stefanofinetti/MF_RMP_Panel/3D FIles/V5.1/CopriLed-CopriLed-1.5mm.stl

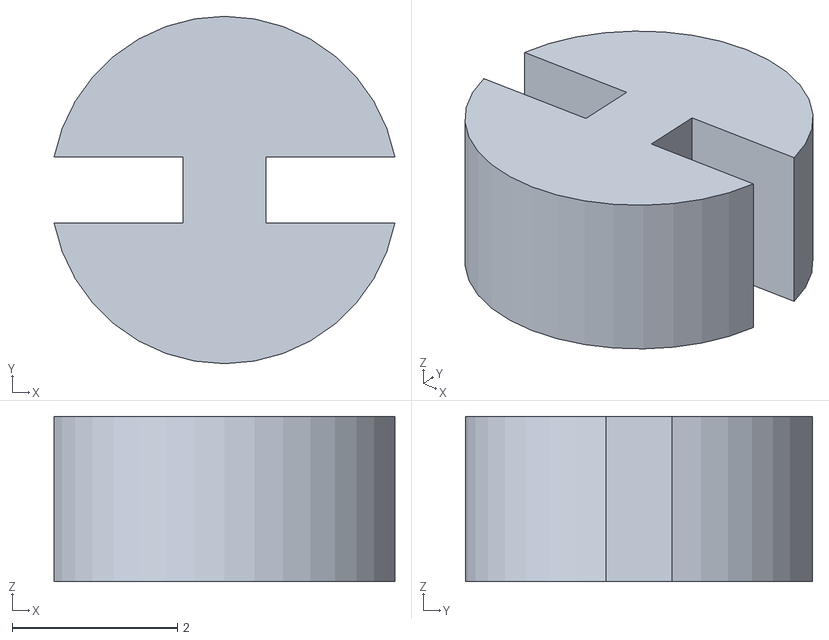
[picture p27: CAD file, 2026-10-05]
3D FIles/V5.1/CopriLed-CopriLed-1.5mm.stl
4.12 x 4.20 x 2.00
