stefanofinetti/MF_RMP_Panel/3D FIles/RMP_Panel-StandbyDisplayCase.stl

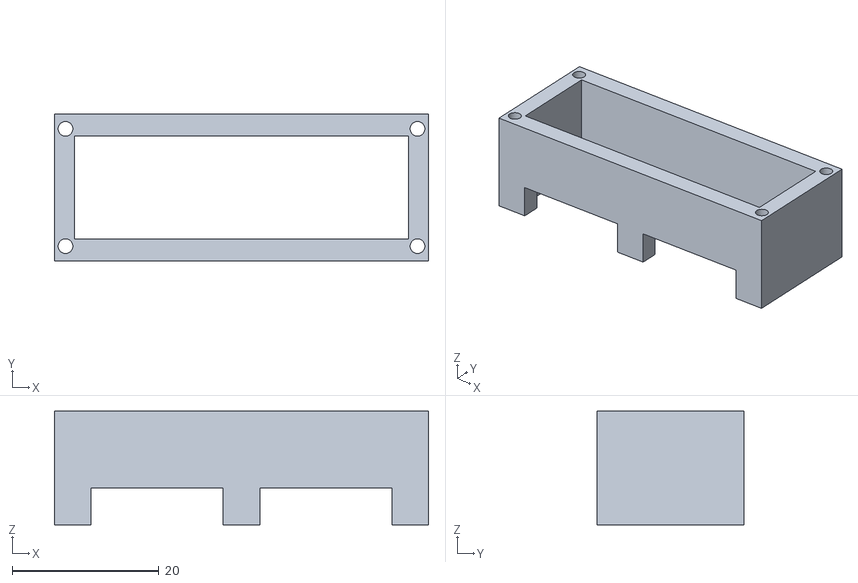
[picture p29: CAD file, 2026-10-05]
3D FIles/RMP_Panel-StandbyDisplayCase.stl
51.0 x 20.0 x 15.5
