stefanofinetti/MF_RMP_Panel/3D FIles/V5.1/RMP_Knob-LowerCircle_KHz.stl

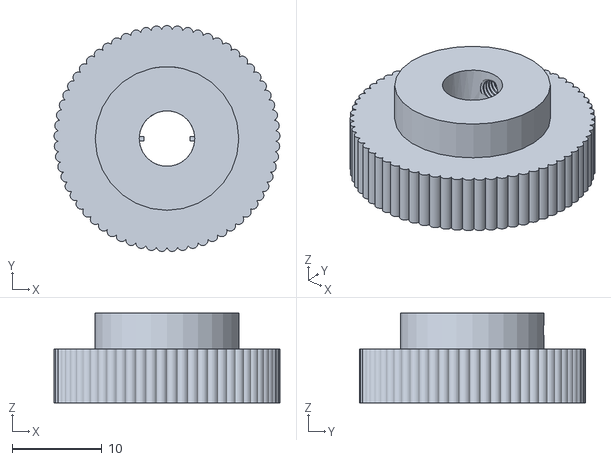
[picture p30: CAD file, 2026-10-05]
3D FIles/V5.1/RMP_Knob-LowerCircle_KHz.stl
25.2 x 25.2 x 10.0
