stefanofinetti/MF_RMP_Panel/3D FIles/RMP_Panel-Labels.stl

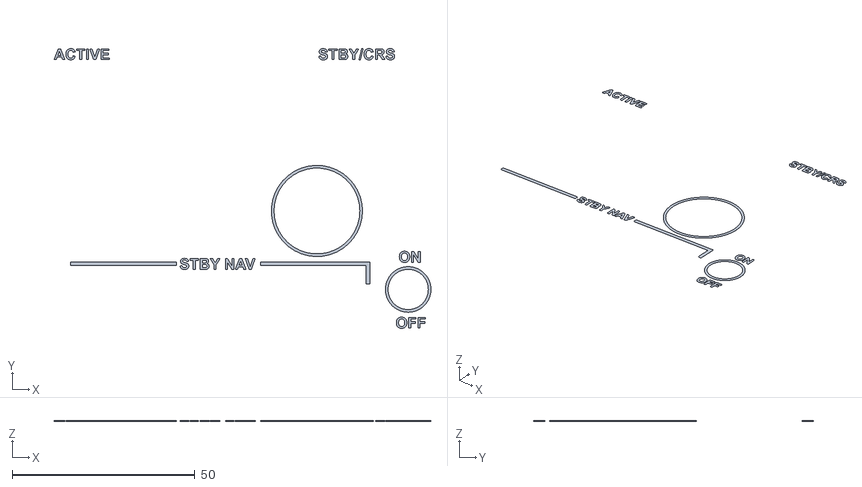
[picture p31: CAD file, 2026-10-05]
3D FIles/RMP_Panel-Labels.stl
103.3 x 76.7 x 0.2
