stefanofinetti/MF_RMP_Panel/3D FIles/RMP_Panel.3mf

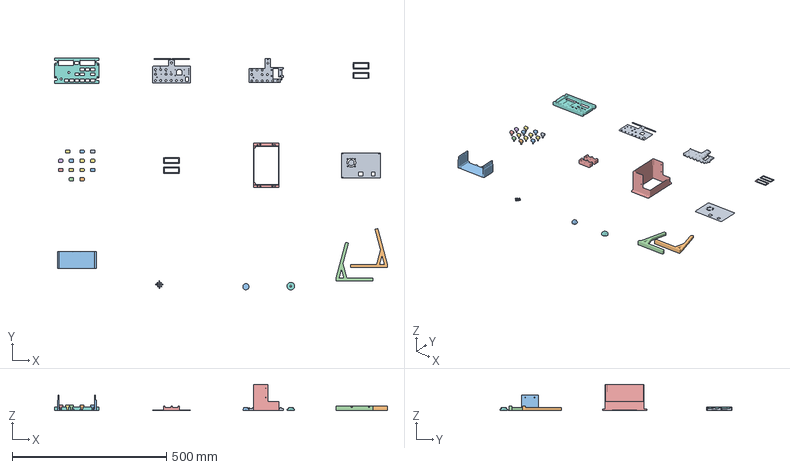
[picture p33: CAD file, 2026-10-05]
3D FIles/RMP_Panel.3mf
1079.3 x 752.2 x 85.0 mm
RMP_Button- ADF Black Parts
RMP_Panel-BasePad076 x 2
RMP_Knob-UpperCircle_MHz.stl
RMP_Panel-RMP Case.stl
CopriLed-CopriLed-1.5mm.stl x 13
VHF1_Button-Black Parts
RMP_Panel-RMP Bottom (USB and power holes).stl
RMP_Button- VOR Black Parts
RMP_Panel-ActiveDisplayCase.stl
RMP_Button- BFO Black Parts
RMP_Panel-Led Mask (print x2).stl x 2
RMP_Button-VHF2 Black Parts
RMP_Panel-StandbyDisplayCase.stl
RMP_Button-XFER Black Parts
RMP_Panel-LED PCB.stl
RMP_Button-VHF3 Black Parts
RMP_Button-HF1 Black Parts
RMP_Knob-LowerCircle_KHz.stl
RMP_Panel-PCB Separator.stl
RMP_Button-HF2 Black Parts
RMP_Panel-ArduinoSupport.stl
RMP_Button-AM Black Parts
RMP_Button-NAV Black Parts
RMP_Button-ILS Black Parts
RMP_Button-MLS BlackParts
RMP_Panel-BlackElements
