stefanofinetti/MF_RMP_Panel/3D FIles/V5.1/RMP_Panel-TransparentElements.stl

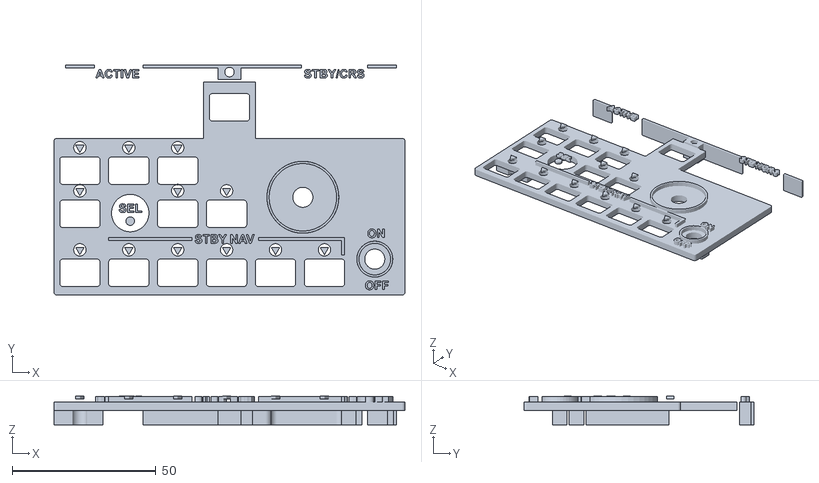
[picture p34: CAD file, 2026-10-05]
3D FIles/V5.1/RMP_Panel-TransparentElements.stl
122.0 x 80.0 x 10.0
