stefanofinetti/MF_RMP_Panel/3D FIles/Buttons/RMP_Button- BFO White Parts.stl

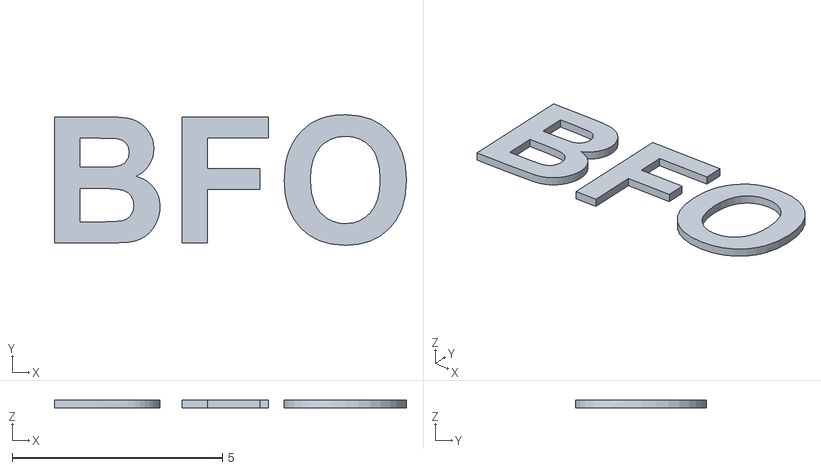
[picture p35: CAD file, 2026-10-05]
3D FIles/Buttons/RMP_Button- BFO White Parts.stl
8.36 x 3.10 x 0.2
