stefanofinetti/MF_RMP_Panel/3D FIles/Labels.stl

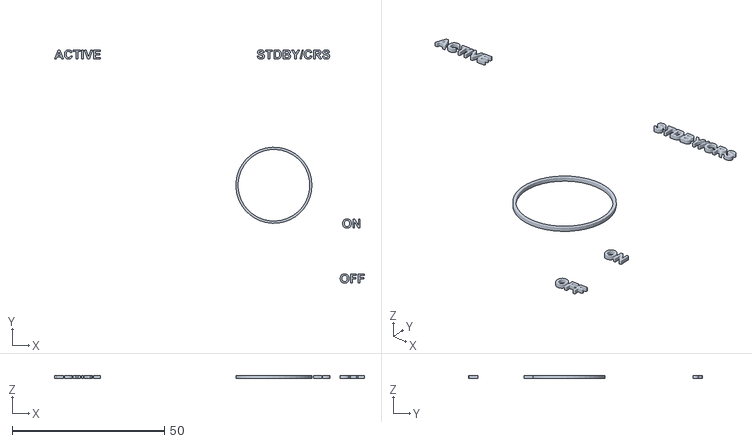
[picture p36: CAD file, 2026-10-05]
3D FIles/Labels.stl
101.8 x 76.7 x 1.00
