stefanofinetti/MF_RMP_Panel/3D FIles/Buttons/RMP_Button-XFER White Parts.stl

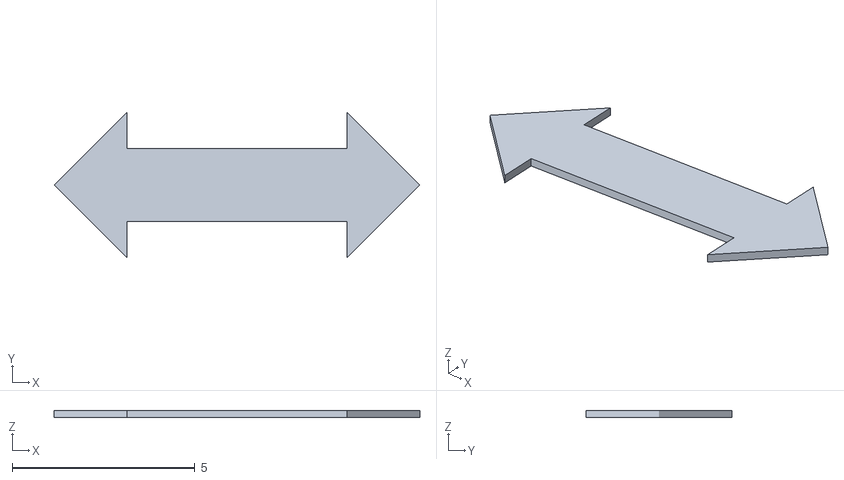
[picture p37: CAD file, 2026-10-05]
3D FIles/Buttons/RMP_Button-XFER White Parts.stl
10.0 x 4.00 x 0.2
