stefanofinetti/MF_RMP_Panel/3D FIles/RMP_Panel-LED PCB.stl

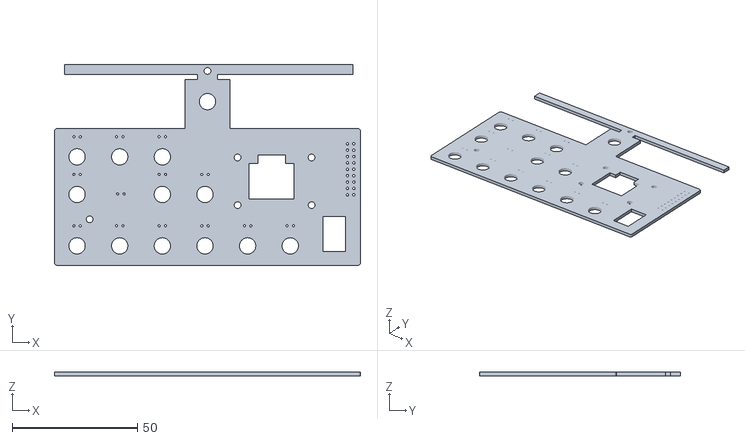
[picture p38: CAD file, 2026-10-05]
3D FIles/RMP_Panel-LED PCB.stl
122.0 x 80.0 x 1.51
