stefanofinetti/MF_RMP_Panel/3D FIles/Buttons/RMP_Button-NAV White Parts.stl

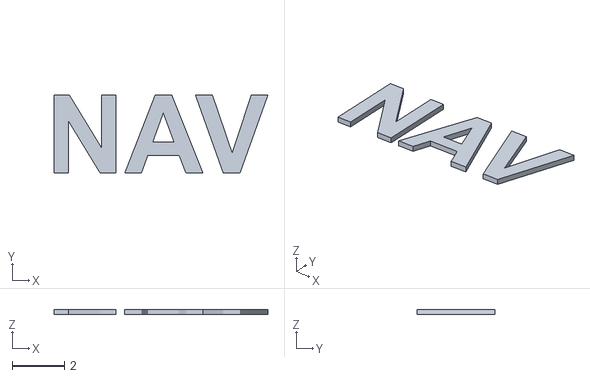
[picture p39: CAD file, 2026-10-05]
3D FIles/Buttons/RMP_Button-NAV White Parts.stl
8.22 x 3.00 x 0.2
