stefanofinetti/MF_RMP_Panel/3D FIles/RMP_Panel-TransparentElements.stl

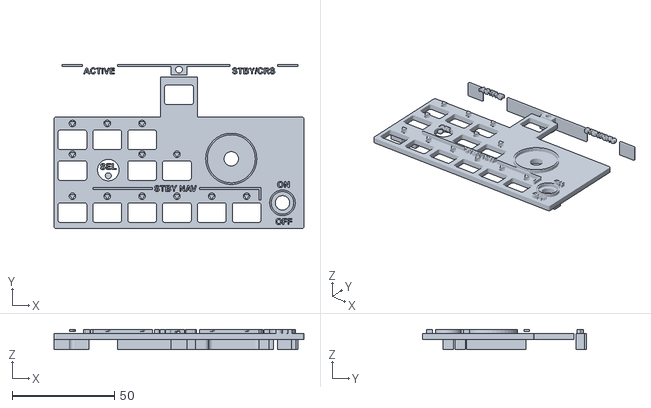
[picture p40: CAD file, 2026-10-05]
3D FIles/RMP_Panel-TransparentElements.stl
122.0 x 80.0 x 10.0
