stefanofinetti/MF_RMP_Panel/3D FIles/RMP_Button.FCStd

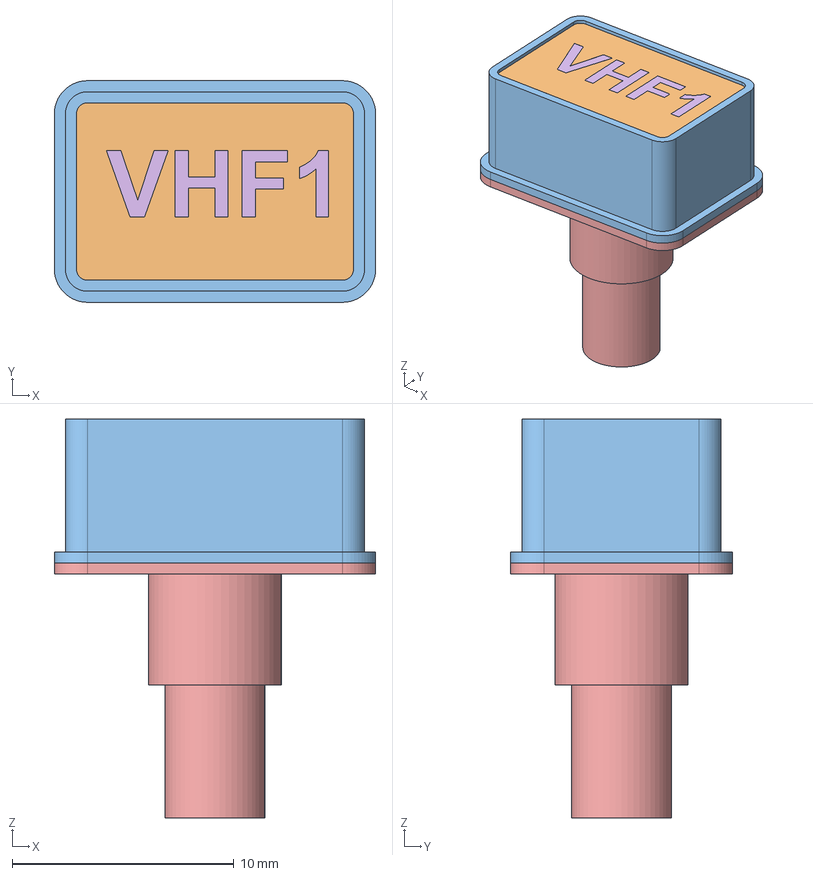
[picture p41: CAD file, 2026-10-05]
3D FIles/RMP_Button.FCStd
14.5 x 10.0 x 18.0 mm
Button Upper Layer
Cutout
Button Casing
LabelTransparent
Button Transparent Block
LabelWhite
