stefanofinetti/MF_RMP_Panel/3D FIles/V5.1/RMP_Panel-Left SupportPad075.stl

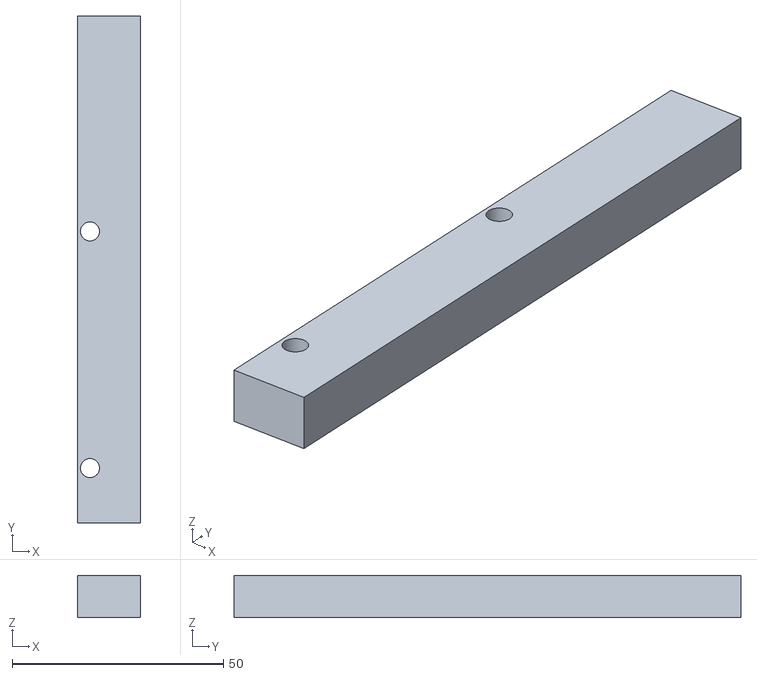
[picture p42: CAD file, 2026-10-05]
3D FIles/V5.1/RMP_Panel-Left SupportPad075.stl
15.0 x 120.0 x 10.0
