stefanofinetti/MF_RMP_Panel/3D FIles/RMP_Panel-Led Mask (print x2).stl

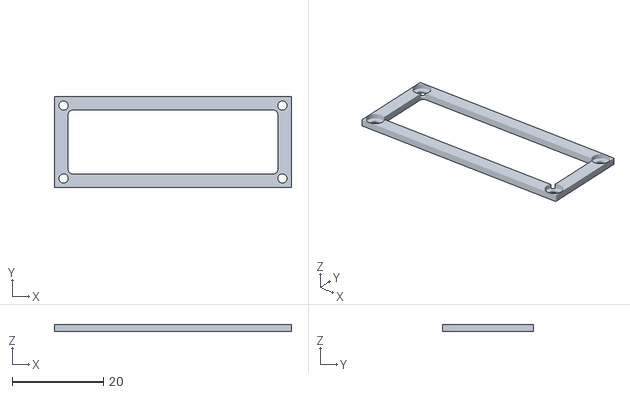
[picture p44: CAD file, 2026-10-05]
3D FIles/RMP_Panel-Led Mask (print x2).stl
52.0 x 20.0 x 1.50
