stefanofinetti/MF_RMP_Panel/3D FIles/V5.1/RMP_Panel-BasePad076.stl

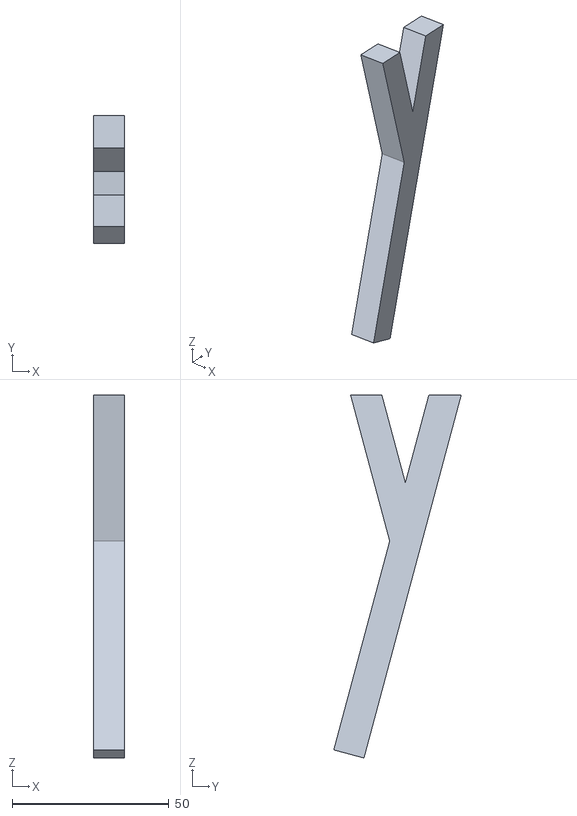
[picture p45: CAD file, 2026-10-05]
3D FIles/V5.1/RMP_Panel-BasePad076.stl
10.0 x 40.7 x 115.9
