stefanofinetti/MF_RMP_Panel/3D FIles/Buttons/RMP_Button-HF2 Black Parts.stl

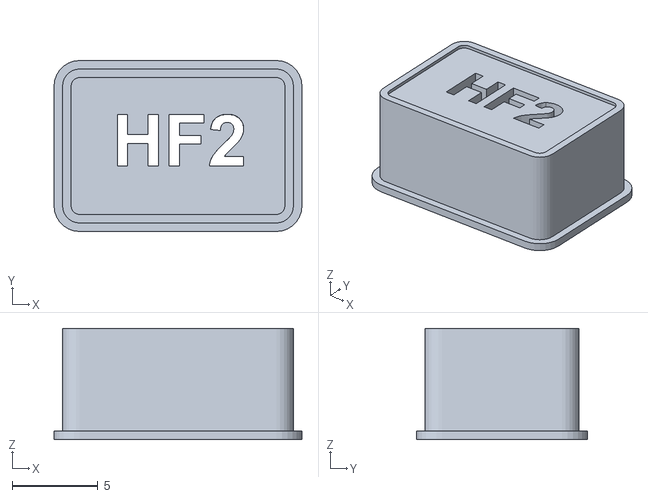
[picture p46: CAD file, 2026-10-05]
3D FIles/Buttons/RMP_Button-HF2 Black Parts.stl
14.5 x 10.0 x 6.50
