stefanofinetti/MF_RMP_Panel/3D FIles/RMP_LEDS1.FCStd

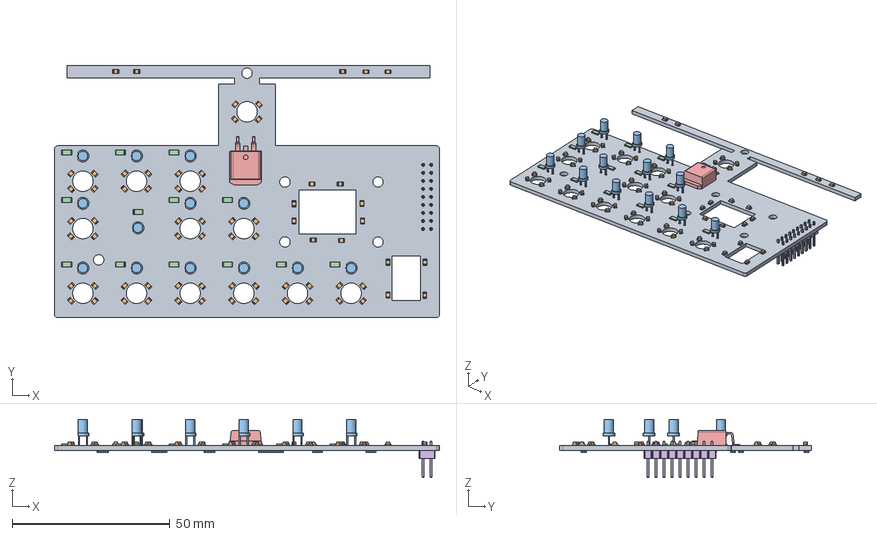
[picture p47: CAD file, 2026-10-05]
3D FIles/RMP_LEDS1.FCStd
122.0 x 80.0 x 18.4 mm
Pcb_f16.[solid]
D20_LED_0805_2012Metric_1352afc11da3 x 69
D74_LED_D3.0mm_FlatTop_4eb7fb95d653 x 13
R25_R_1206_3216Metric_ccd3cef4aefe x 29
Q1_IRLZ44NSTRLPBF_374ea2df2183
J1_PinHeader_2x09_P254mm_Vertical_5930f4462cf5
