stefanofinetti/MF_RMP_Panel/3D FIles/Buttons/RMP_Button-HF2 White Parts.stl

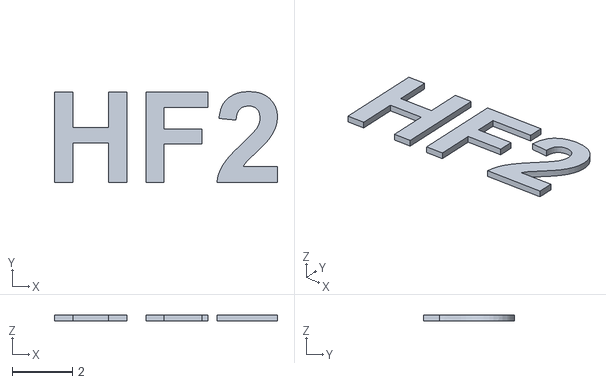
[picture p48: CAD file, 2026-10-05]
3D FIles/Buttons/RMP_Button-HF2 White Parts.stl
7.39 x 3.02 x 0.2
