stefanofinetti/MF_RMP_Panel/3D FIles/FrontPanelWithWritings.stl

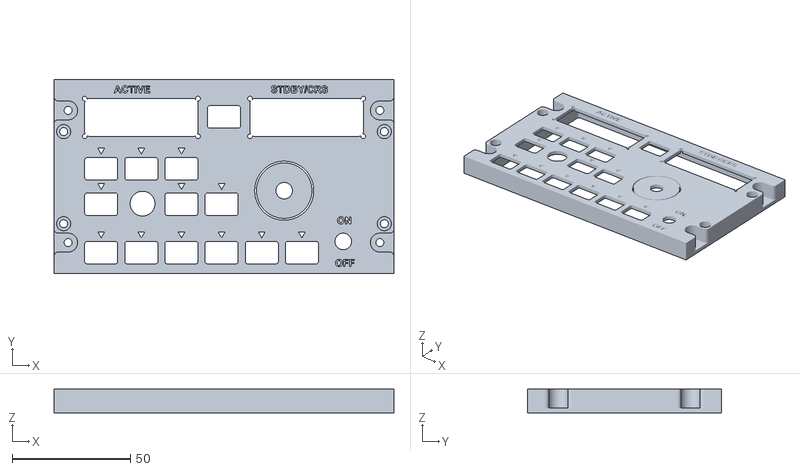
[picture p49: CAD file, 2026-10-05]
3D FIles/FrontPanelWithWritings.stl
144.0 x 82.0 x 10.0
