stefanofinetti/MF_RMP_Panel/3D FIles/Buttons/RMP_Button-VHF2 Transparent Parts.stl

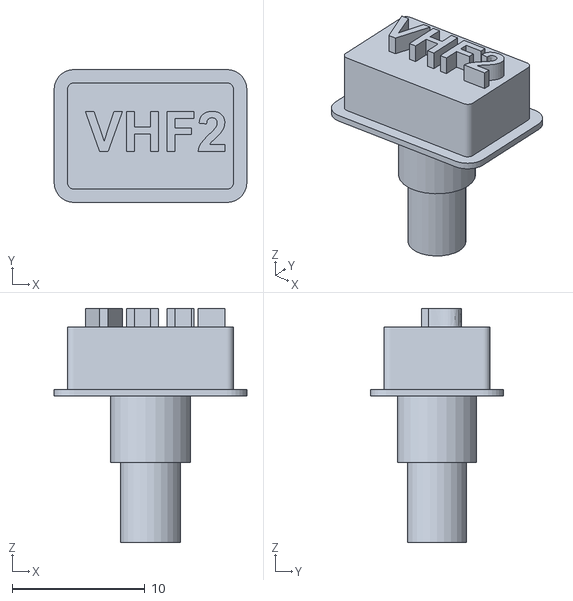
[picture p50: CAD file, 2026-10-05]
3D FIles/Buttons/RMP_Button-VHF2 Transparent Parts.stl
14.5 x 10.0 x 17.6
