stefanofinetti/MF_RMP_Panel/3D FIles/Buttons/RMP_Button- VOR White Parts.stl

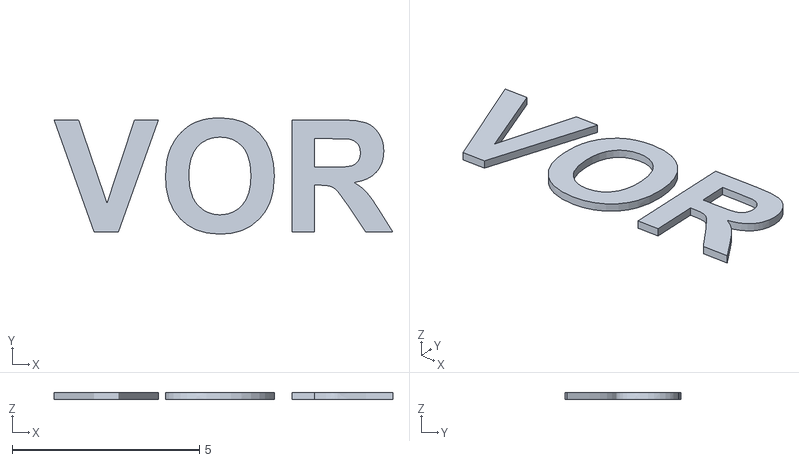
[picture p51: CAD file, 2026-10-05]
3D FIles/Buttons/RMP_Button- VOR White Parts.stl
9.05 x 3.10 x 0.2
