stefanofinetti/MF_RMP_Panel/3D FIles/Buttons/RMP_Button-ILS White Parts.stl

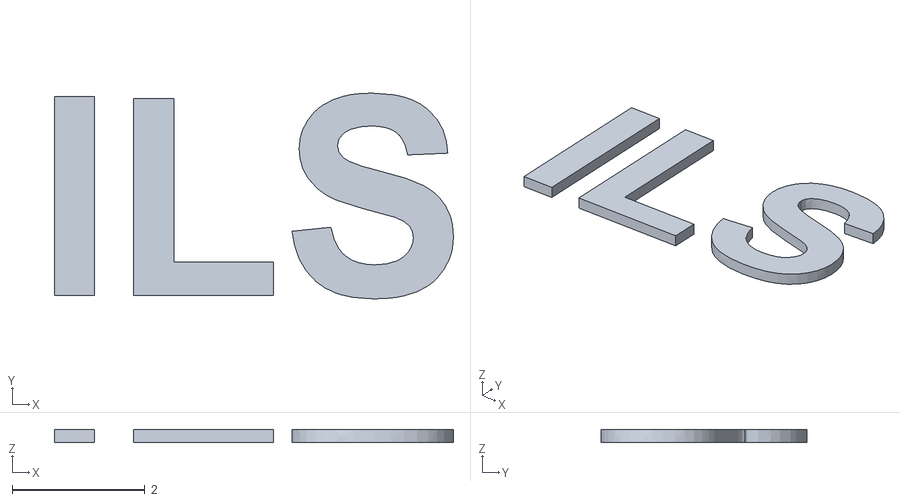
[picture p52: CAD file, 2026-10-05]
3D FIles/Buttons/RMP_Button-ILS White Parts.stl
6.02 x 3.10 x 0.2
