stefanofinetti/MF_RMP_Panel/3D FIles/Buttons/RMP_Button-MLS White Parts.stl

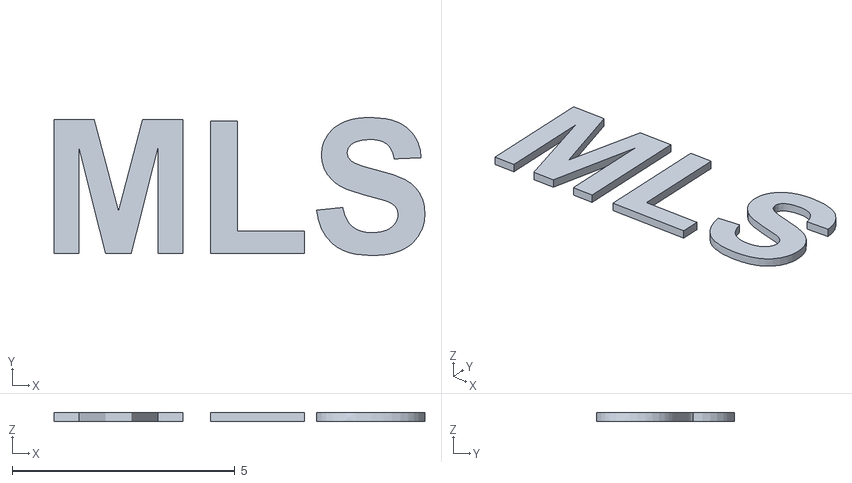
[picture p54: CAD file, 2026-10-05]
3D FIles/Buttons/RMP_Button-MLS White Parts.stl
8.33 x 3.10 x 0.2
