stefanofinetti/MF_RMP_Panel/3D FIles/Buttons/RMP_Button-HF1 WhiteParts.stl

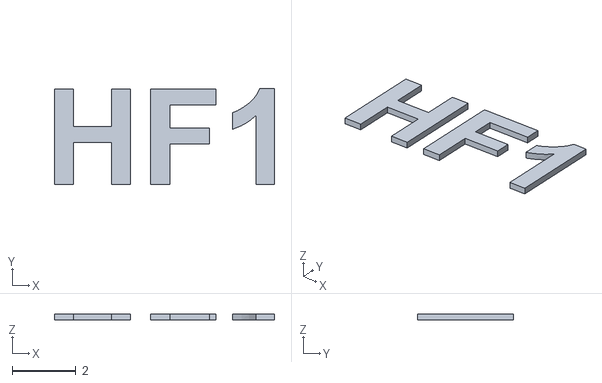
[picture p55: CAD file, 2026-10-05]
3D FIles/Buttons/RMP_Button-HF1 WhiteParts.stl
6.92 x 3.02 x 0.2
