stefanofinetti/MF_RMP_Panel/3D FIles/Buttons/RMP_Button-NAV Transparent Parts.stl

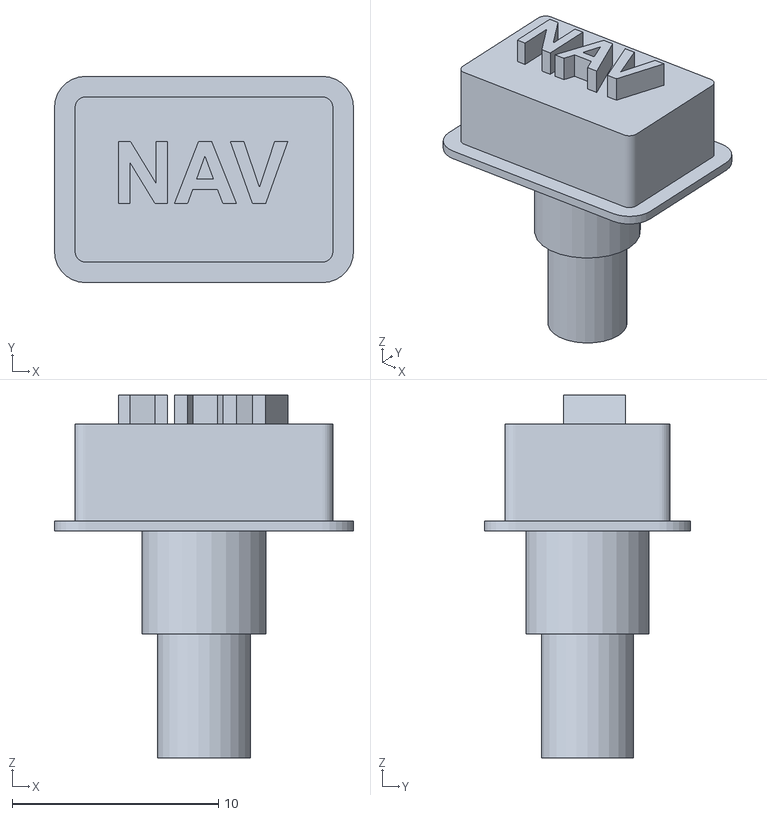
[picture p56: CAD file, 2026-10-05]
3D FIles/Buttons/RMP_Button-NAV Transparent Parts.stl
14.5 x 10.0 x 17.6
