stefanofinetti/MF_RMP_Panel/3D FIles/Buttons/RMP_Button-VHF2 White Parts.stl

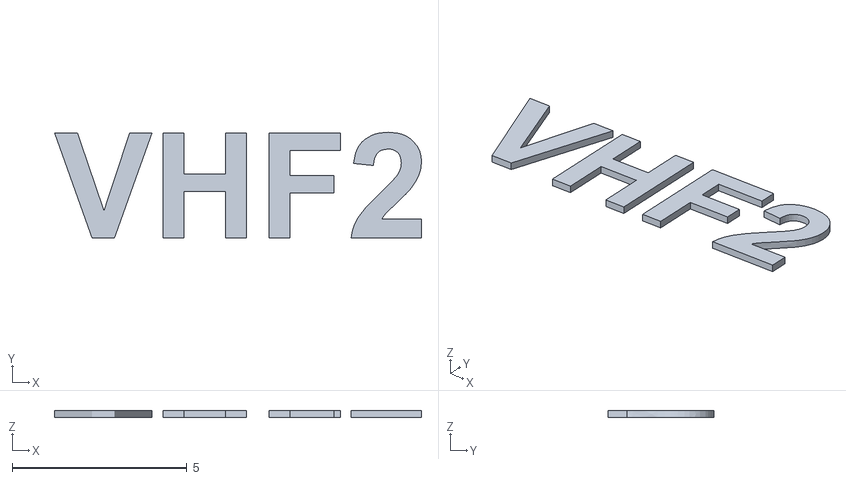
[picture p57: CAD file, 2026-10-05]
3D FIles/Buttons/RMP_Button-VHF2 White Parts.stl
10.5 x 3.02 x 0.2
